lukasz-tuz/kids-control-panel/export/IMG_20210217_094639671.jpg

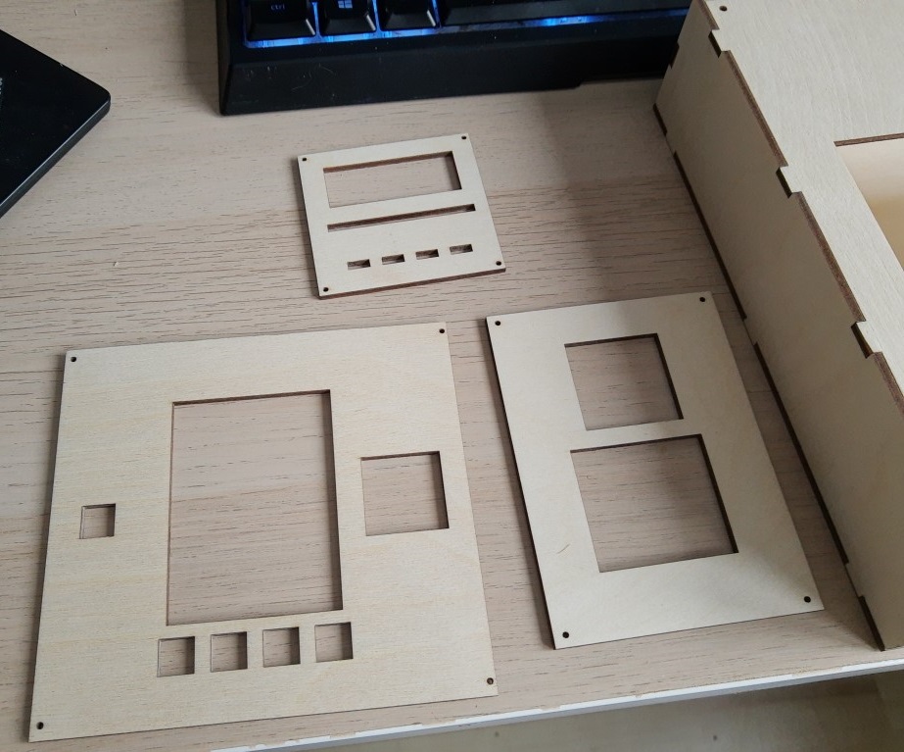
export/IMG_20210217_094639671.jpg
