lukasz-tuz/kids-control-panel/export/IMG_20210217_094712894.jpg

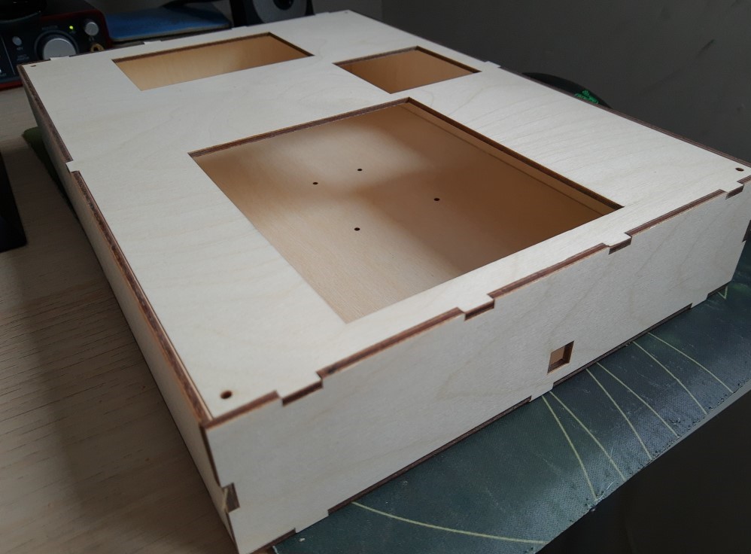
export/IMG_20210217_094712894.jpg
