lukasz-tuz/kids-control-panel/export/IMG_20210217_094746303.jpg

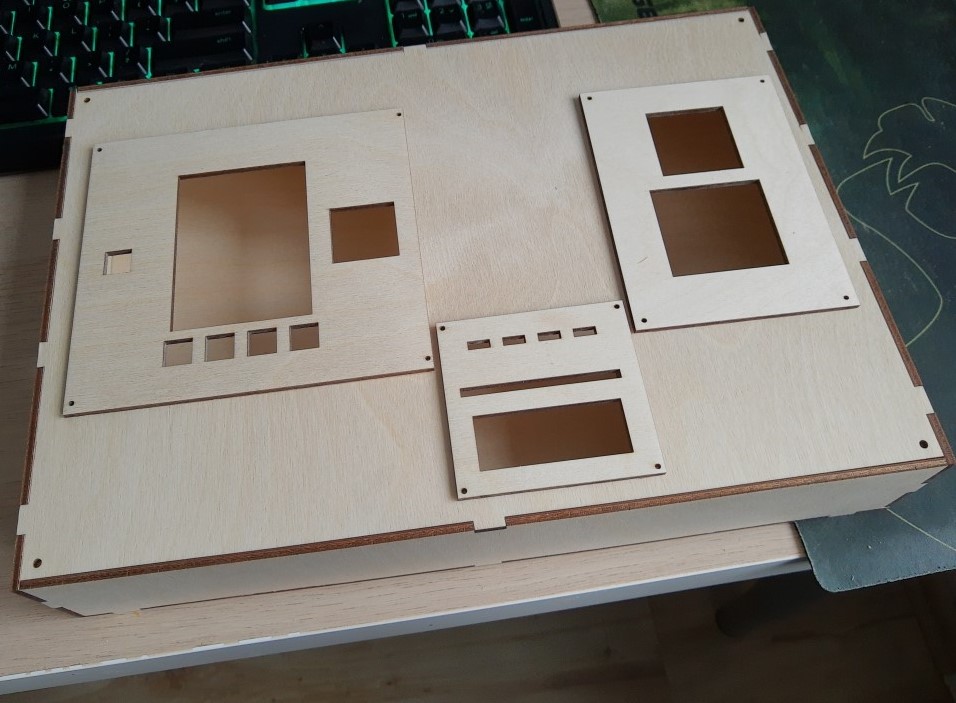
export/IMG_20210217_094746303.jpg
