lukasz-tuz/kids-control-panel/export/IMG_20210217_210604149.jpg

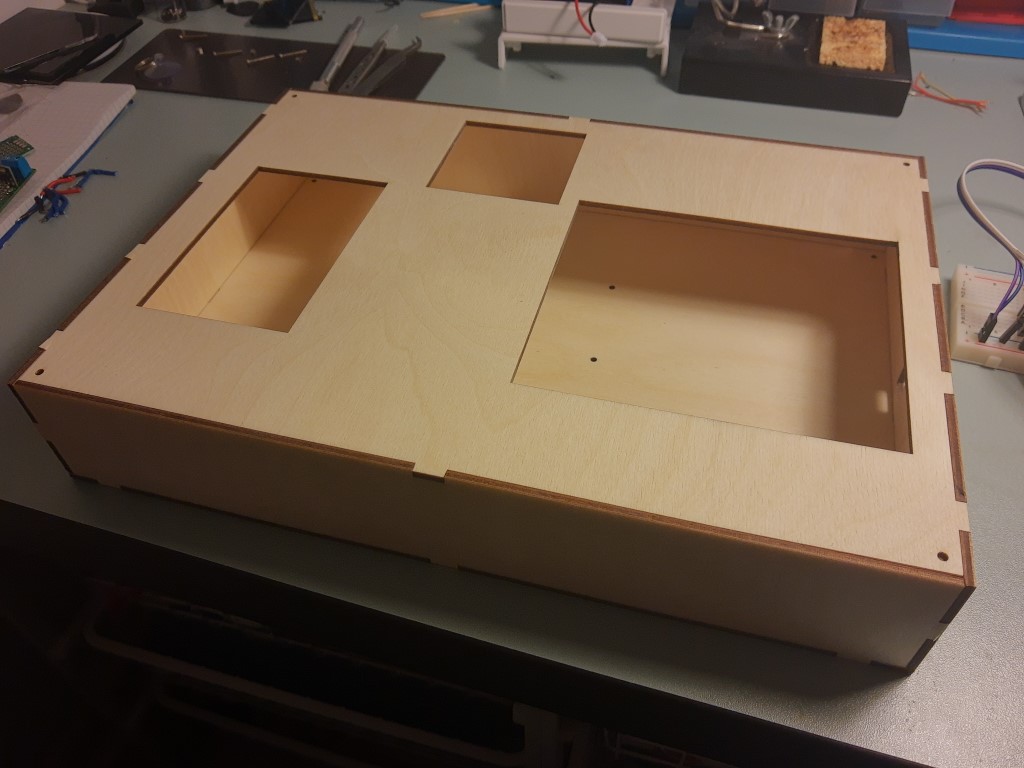
export/IMG_20210217_210604149.jpg
