lukasz-tuz/kids-control-panel/export/IMG_20210419_174134030.jpg

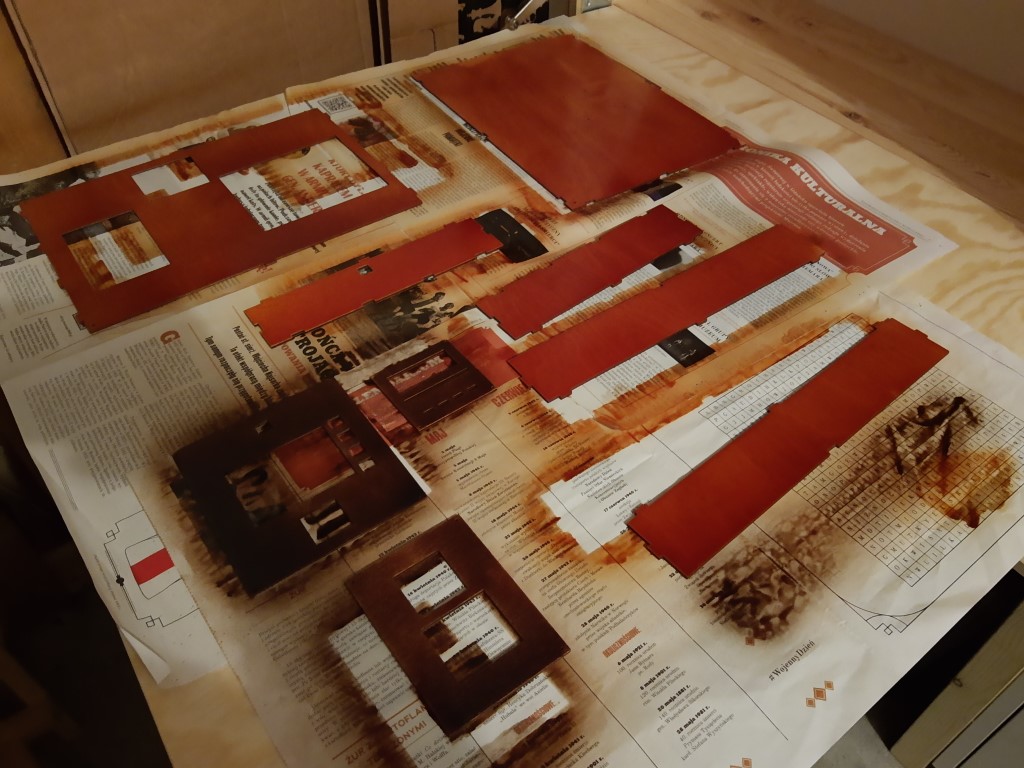
export/IMG_20210419_174134030.jpg
