lukasz-tuz/kids-control-panel/export/IMG_20210423_223901926.jpg

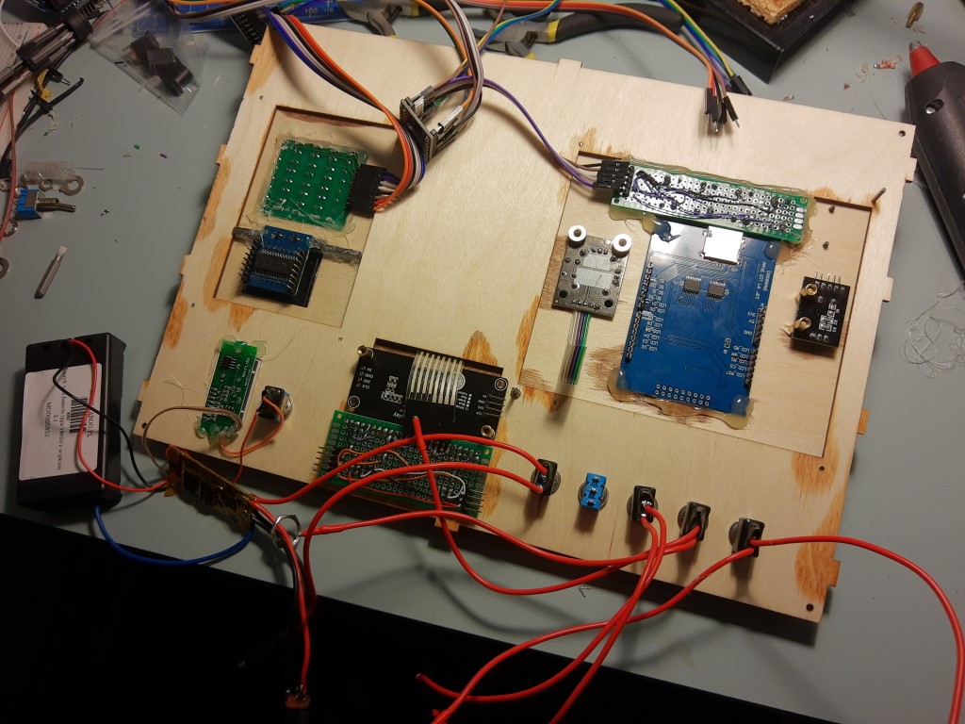
export/IMG_20210423_223901926.jpg
