lukasz-tuz/kids-control-panel/export/IMG_20210429_121035189.jpg

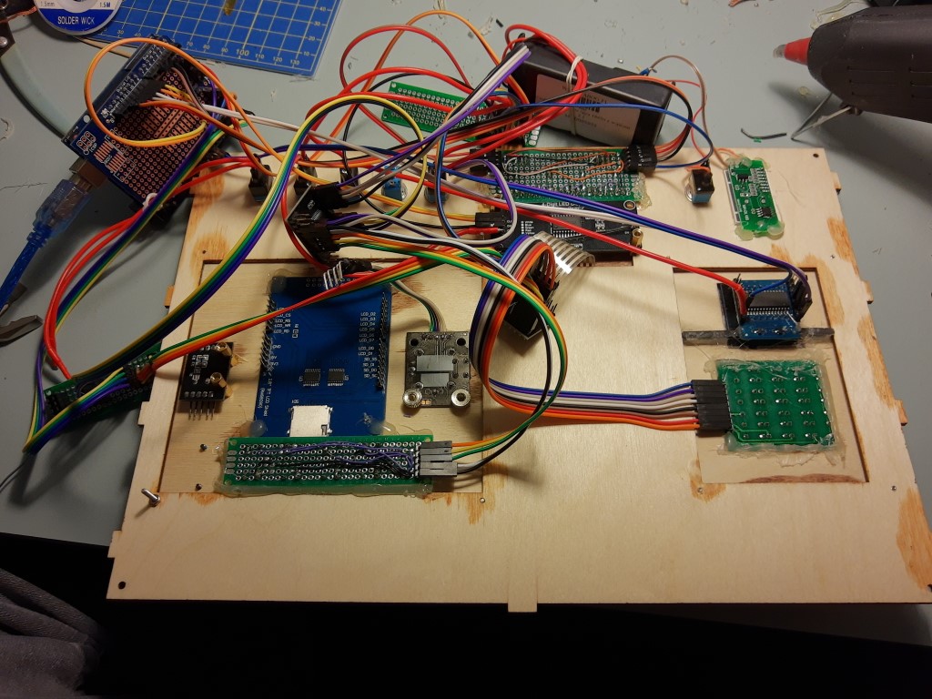
export/IMG_20210429_121035189.jpg
