lukasz-tuz/kids-control-panel/export/IMG_20210430_230025312.jpg

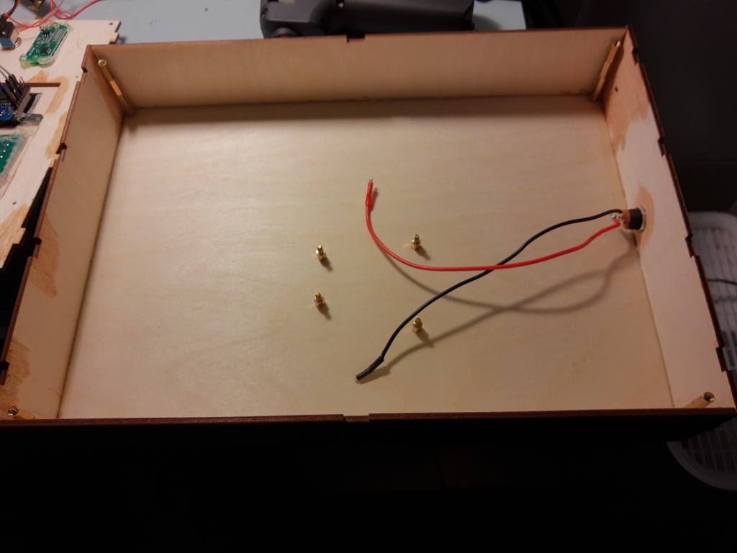
export/IMG_20210430_230025312.jpg
