lukasz-tuz/kids-control-panel/export/IMG_20210430_230030190.jpg

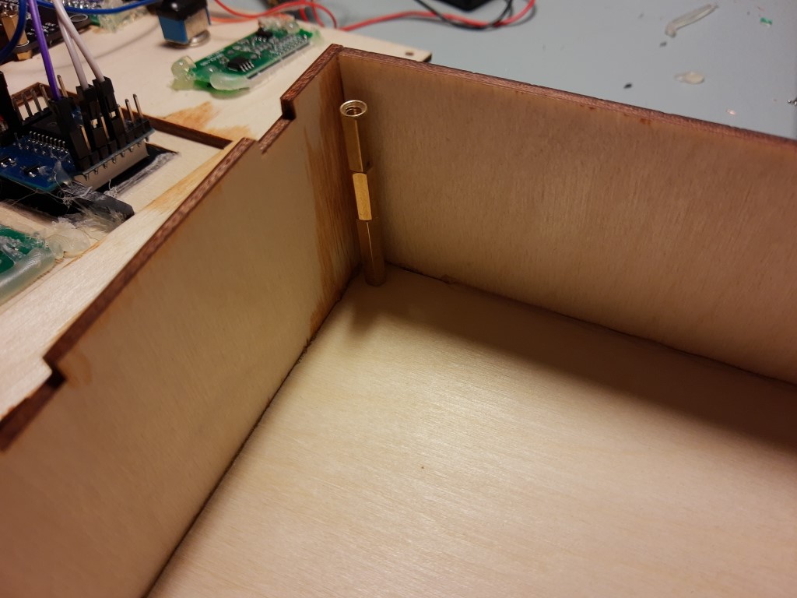
export/IMG_20210430_230030190.jpg
