lukasz-tuz/kids-control-panel/export/IMG_20210430_230052931.jpg

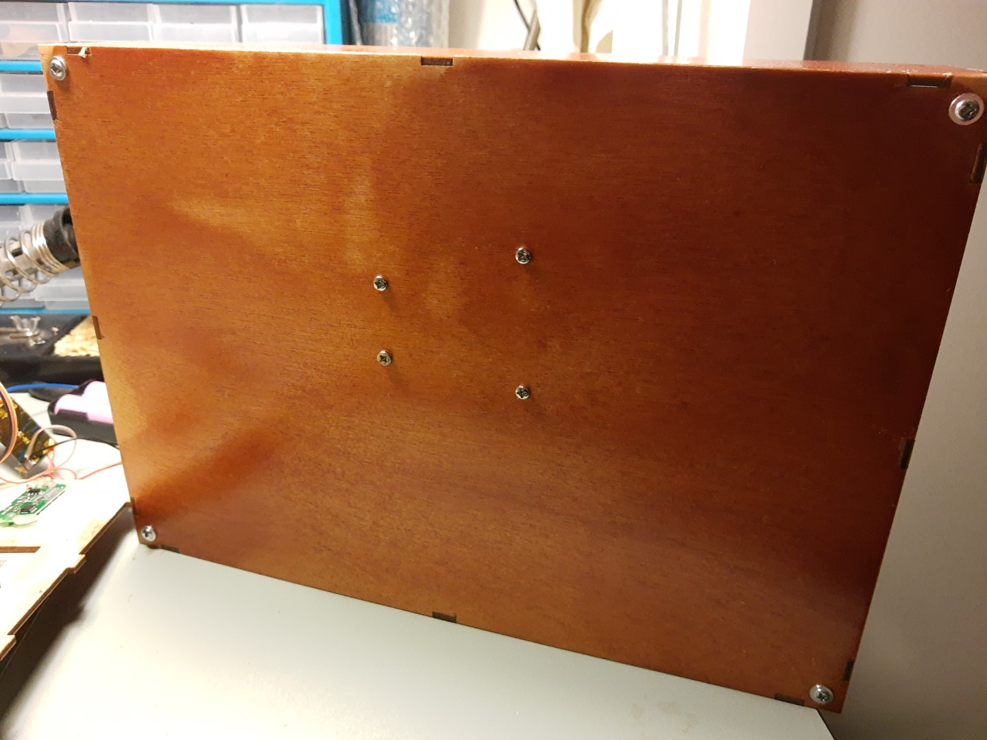
export/IMG_20210430_230052931.jpg
