lukasz-tuz/kids-control-panel/export/IMG_20210430_232541585.jpg

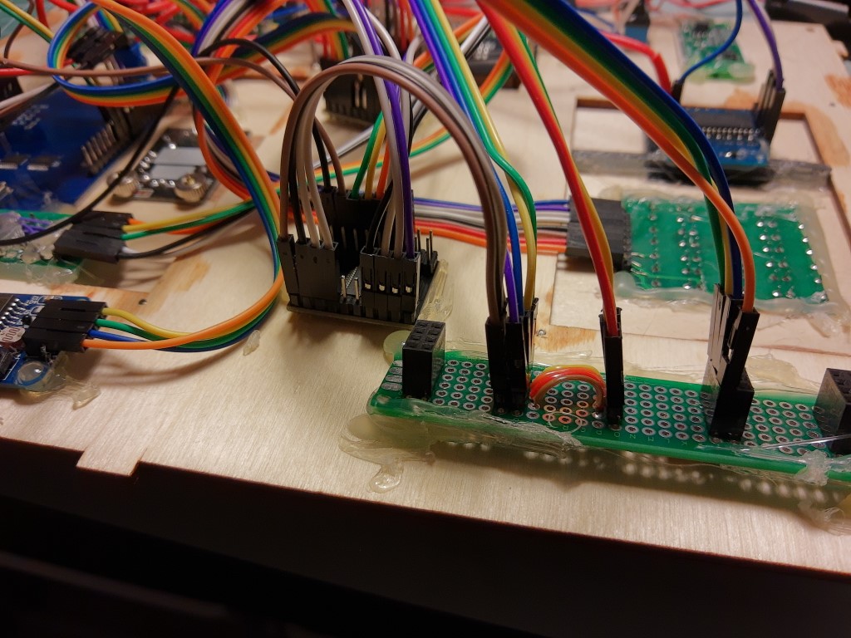
export/IMG_20210430_232541585.jpg
