lukasz-tuz/kids-control-panel/export/IMG_20210430_232549553.jpg

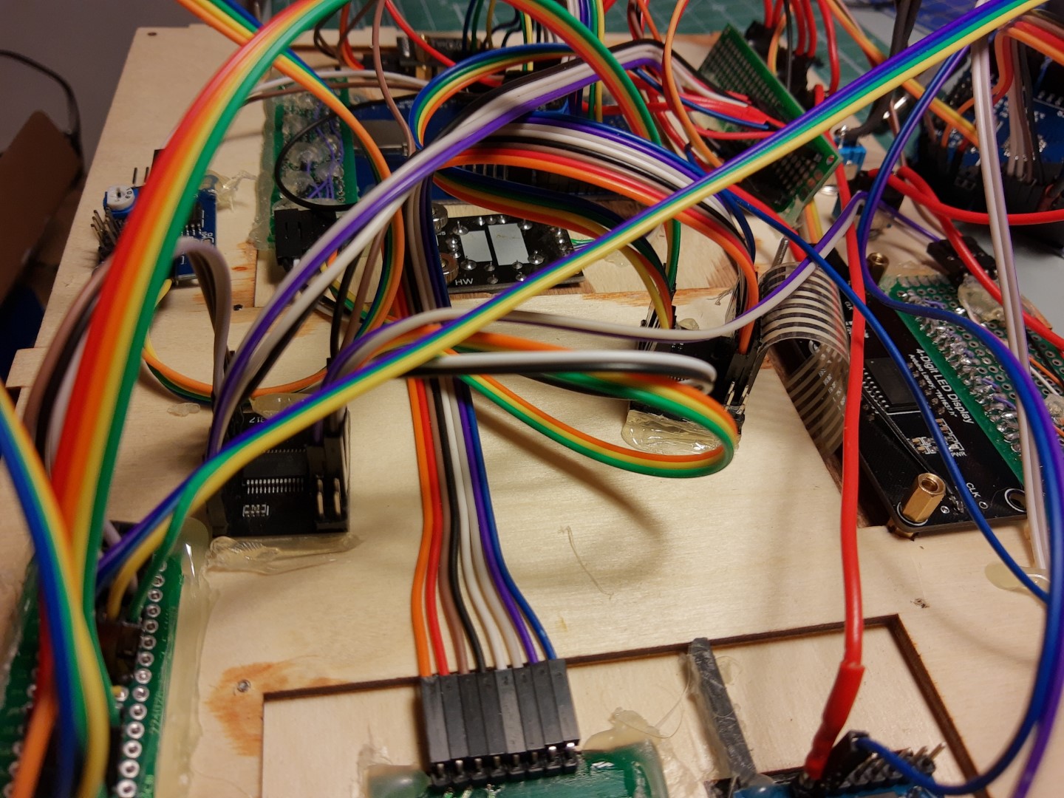
export/IMG_20210430_232549553.jpg
