lukasz-tuz/kids-control-panel/export/IMG_20210430_232554605.jpg

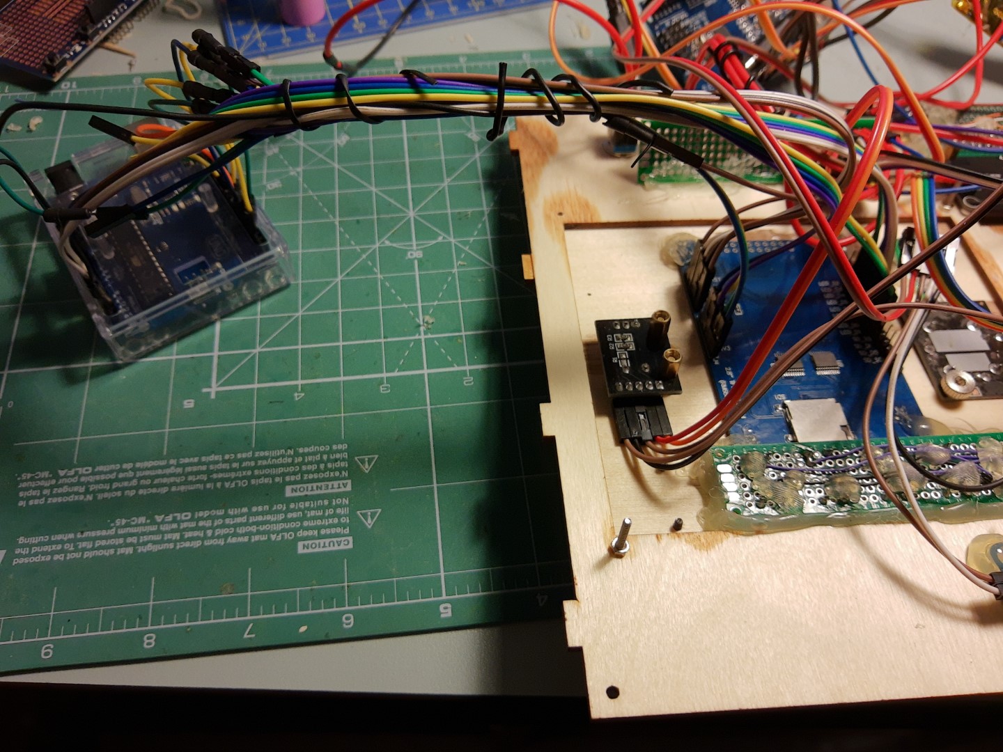
export/IMG_20210430_232554605.jpg
