lukasz-tuz/kids-control-panel/export/IMG_20210501_070627496.jpg

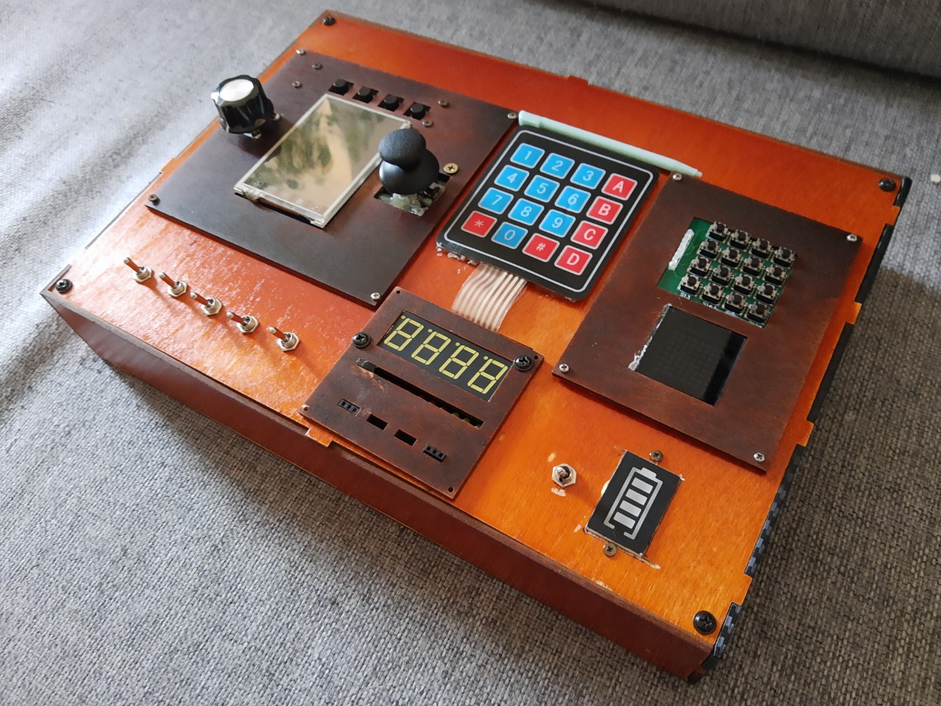
export/IMG_20210501_070627496.jpg
