lukasz-tuz/kids-control-panel/export/IMG_20210501_070836978.jpg

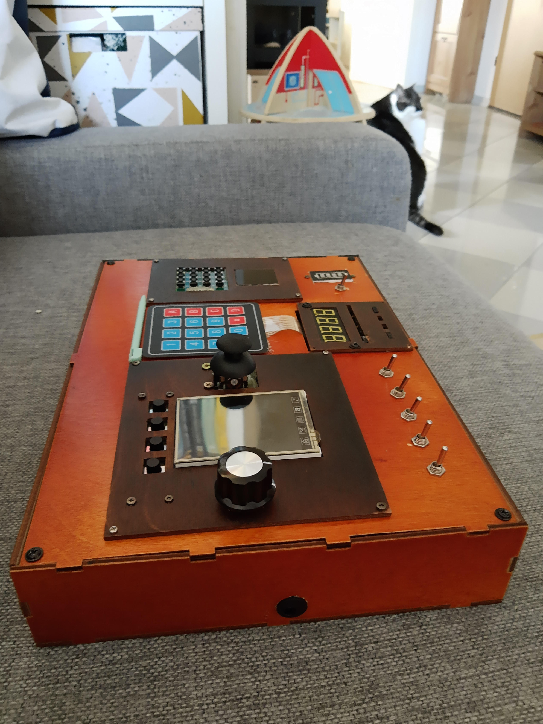
export/IMG_20210501_070836978.jpg
