lukasz-tuz/kids-control-panel/export/xy2rgb wheel.png

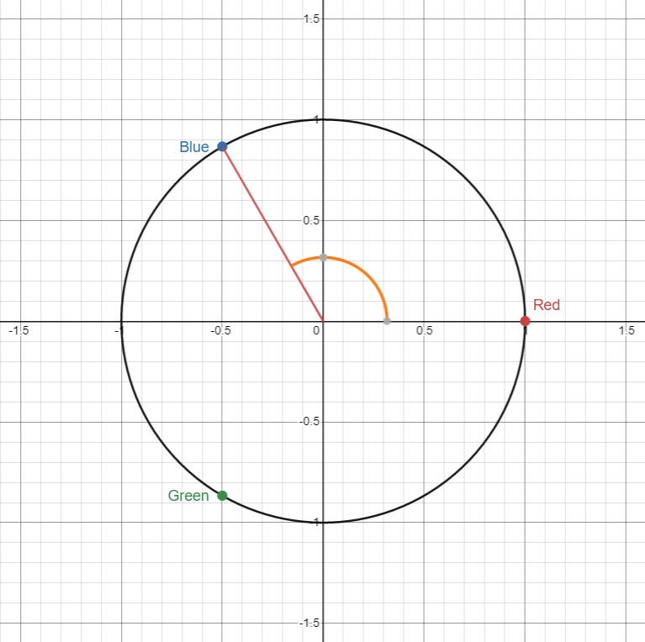
export/xy2rgb wheel.png
